cr1tbit/cringenode/MOSNode-fw/include/pinDefs.h

#pragma once

#define ESP_TX 21
#define ESP_RX 20

#define IO0 0
#define IO1 1
#define IO2 2
#define IO3_BUT3 3
#define IO4_LED 4
#define IO4_LED_CCISR 4
#define IO5_SCL 5
#define IO6_SDA 6
#define IO7_GATEIN 7
#define IO8_BUT2 8
#define IO9_BUT1 9
#define IO10 10

#define SHUNT_IN_RES_MR 25
#define SHUNT_1_RES_MR 25
#define SHUNT_2_RES_MR 25
